BenedictS24/ENS-helper-device/images/circuit.png

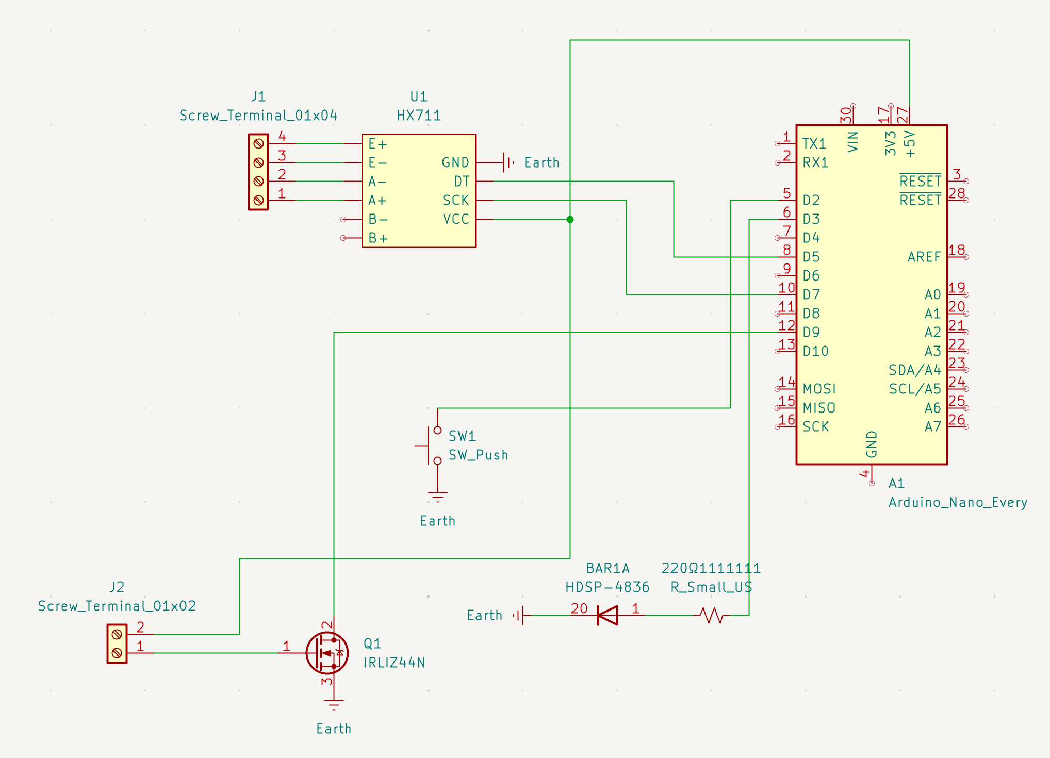
images/circuit.png
