BenedictS24/ENS-helper-device/images/device_worn.JPG

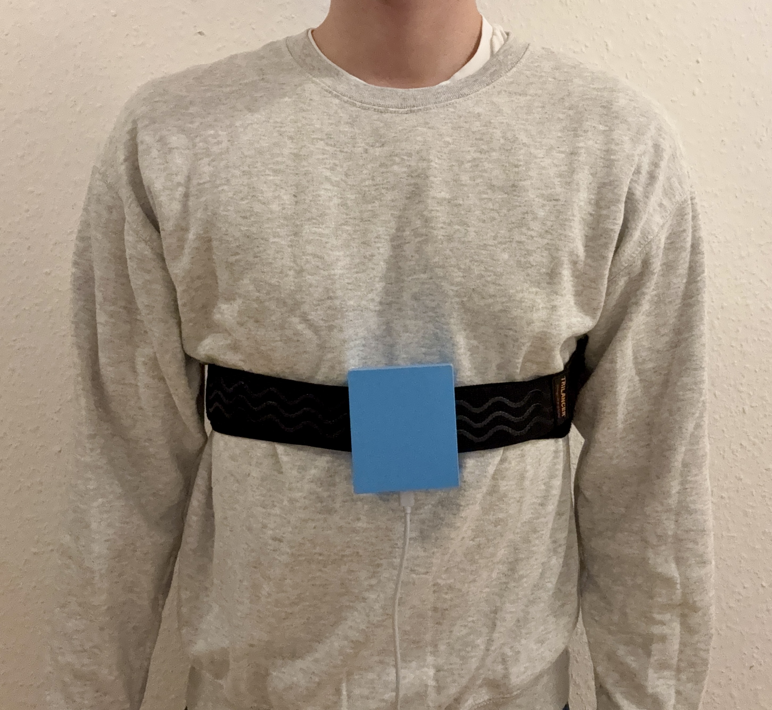
images/device_worn.JPG
