BenedictS24/ENS-helper-device/KiCad/sensory_support_device.kicad_sch

## KiCad design KiCad/sensory_support_device.kicad_sch (2026-01-31)

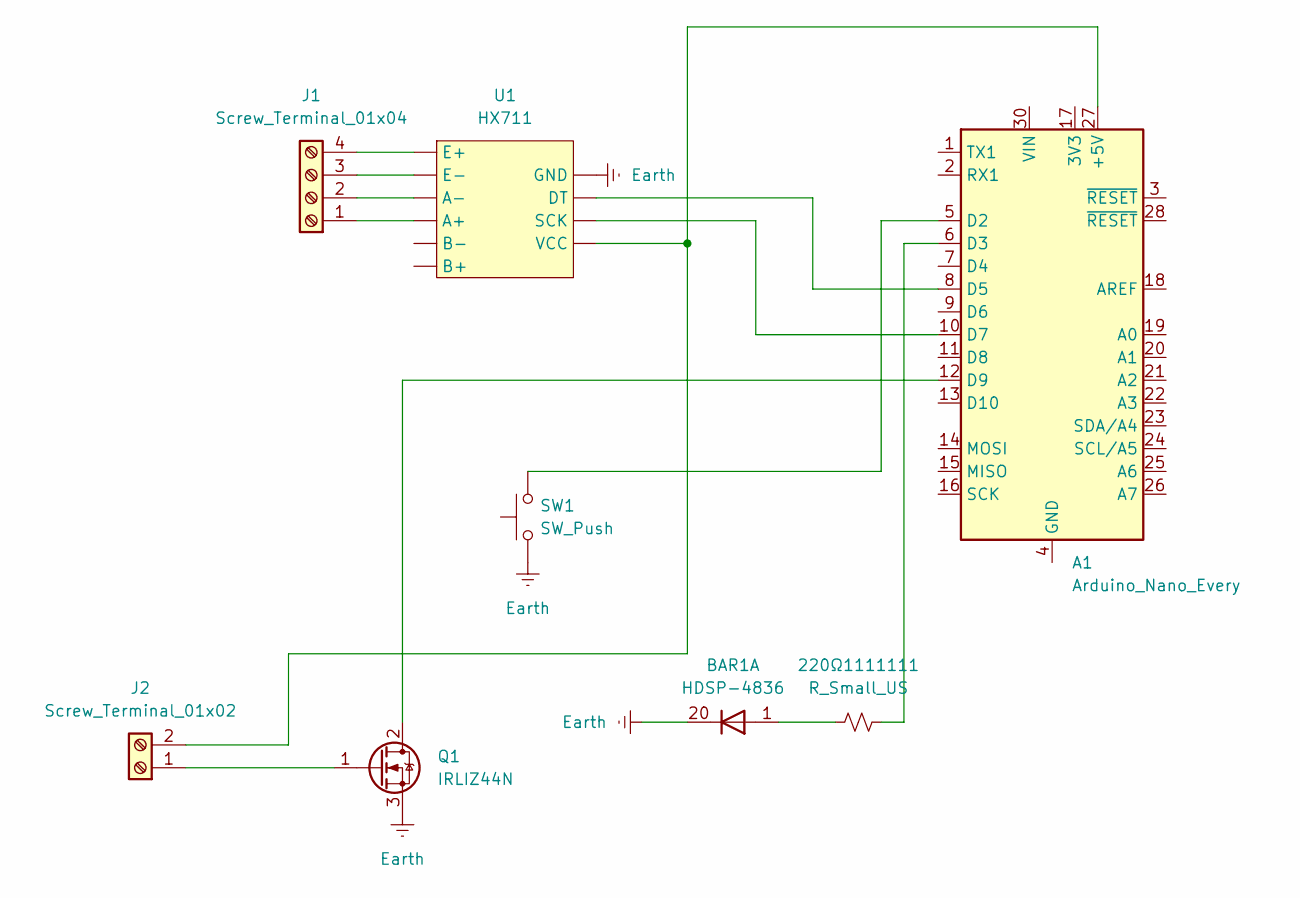
[picture p14: schematic sensory_support_device.kicad_sch]

Parts:
220Ω1111111: R_Small_US
A1: Arduino_Nano_Every; Arduino_Nano
BAR1: HDSP-4836
J1: Screw_Terminal_01x04
J2: Screw_Terminal_01x02
Q1: IRLIZ44N; TO-220F-3_Vertical
SW1: SW_Push
U1: HX711; HX711_Weight_Sensor_Module

Connections:
Earth: BAR1.20 (K), Q1.3 (S), SW1.1, U1.
unnamed: 220Ω1111111.1, BAR1.1 (A)
unnamed: 220Ω1111111.2, A1.6 (D3)
unnamed: A1.5 (D2), SW1.2
unnamed: A1.8 (D5), U1.
unnamed: A1.10 (D7), U1.
unnamed: A1.12 (D9), Q1.2 (D)
unnamed: A1.27 (+5V), J2.2, U1.
unnamed: A1.4 (GND), A1.29 (GND)
unnamed: J1.1, U1.
unnamed: J1.2, U1.
unnamed: J1.3, U1.
unnamed: J1.4, U1.
unnamed: J2.1, Q1.1 (G)
